Bulduper/HexaClock/usermod_v2_hexa_clock/digits.h

//segment for each orientation (6), of each digitSegment (4), of specific led indexes (12 or 13)
const int digitSegment [6][4][13] = 
{
    {
        {
            15,16,33,32,31,35,36,37,54,53,52,60,61
        },
        {
            2,3,12,11,10,18,19,20,29,28,27,39,40
        },
        {
            86,87,99,98,97,106,107,108,116,115,114,123,124
        },
        {
            65,66,74,73,72,89,90,91,95,94,93,110,111
        }
    },
    {
        {
            58,55,80,59,54,79,60,84,78,61,85,77
        },
        {
            16,13,31,17,12,30,18,38,29,19,39,28
        },
        {
            98,87,107,97,88,108,96,114,109,95,113,110
        },
        {
            49,41,65,48,42,66,47,72,67,46,71,68
        }
    }
};

const bool digitMask[2][10][13] = 
{
    {
        {
             1,1,
            1,0,1,
            1,0,1,
            1,0,1,
             1,1
        },
        {
             1,0,
            1,1,0,
            0,1,0,
            0,1,0,
             0,1
        },
        {
             1,1,
            1,0,1,
            0,1,0,
            1,0,1,
             1,1
        },
        {
             1,1,
            1,0,1,
            0,1,1,
            0,0,1,
             1,1
        },
        {
             0,1,
            1,0,1,
            1,1,1,
            0,0,1,
             0,0
        },
        {
             1,1,
            1,0,0,
            1,1,1,
            0,0,1,
             1,1
        },
        {
             1,1,
            1,0,0,
            1,1,1,
            1,0,1,
             1,1
        },
        {
             1,1,
            1,0,1,
            0,0,1,
            0,0,1,
             0,0
        },
        {
             1,1,
            1,0,1,
            1,1,1,
            1,0,1,
             1,1
        },
        {
             1,1,
            1,0,1,
            1,1,1,
            0,0,1,
             1,1
        },
    },
    {
        {
             1,1,
            1,0,1,
             0,0,
            1,0,1,
             1,1
        },
        {
             0,1,
            0,1,0,
             0,1,
            0,1,0,
             0,1
        },
        {
             1,1,
            0,0,1,
             1,1,
            1,0,0,
             1,1
        },
        {
             1,1,
            0,0,1,
             1,1,
            0,0,1,
             1,1
        },
        {
             1,0,
            1,0,1,
             1,1,
            0,0,1,
             0,1
        },
        {
             1,1,
            1,0,0,
             1,1,
            0,0,1,
             1,1
        },
        {
             1,1,
            1,0,0,
             1,1,
            1,0,1,
             1,1
        },
        {
             1,1,
            0,0,1,
             0,1,
            0,1,0,
             1,0
        },
        {
             1,1,
            1,0,1,
             1,1,
            1,0,1,
             1,1
        },
        {
             1,1,
            1,0,1,
             1,1,
            0,0,1,
             1,1
        }
    }
};

const uint8_t roundMap[127] = {63,
51,50,64,75,76,62,
52,38,39,40,49,65,74,88,87,86,77,61,
53,37,30,29,28,27,41,48,66,73,89,96,97,98,99,85,78,60,
54,36,31,17,18,19,20,21,26,42,47,67,72,90,95,109,108,107,106,105,100,84,79,59,
55,35,32,16,13,12,11,10,9,8,22,25,43,46,68,71,91,94,110,113,114,115,116,117,118,104,101,83,80,58,
56,34,33,15,14,0,1,2,3,4,5,6,7,23,24,44,45,69,70,92,93,111,112,126,125,124,123,122,121,120,119,103,102,82,81,57};

const uint8_t verticalMap[127] = {57,81,82,102,103,119,120,
    56,58,80,83,101,104,118,121,
    34,55,59,79,84,100,105,117,122,
    33,35,54,60,78,85,99,106,116,123,
    15,32,36,53,61,77,86,98,107,115,124,
    14,16,31,37,52,62,76,87,97,108,114,125,
    0,13,17,30,38,51,63,75,88,96,109,113,126,
    1,12,18,29,39,50,64,74,89,95,110,112,
    2,11,19,28,40,49,65,73,90,94,111,
    3,10,20,27,41,48,66,72,91,93,
    4,9,21,26,42,47,67,71,92,
    5,8,22,25,43,46,68,70,
    6,7,23,24,44,45,69};
